lafefspietz/noiseotron/3dprint/pluto-bracket-base-drawing.png

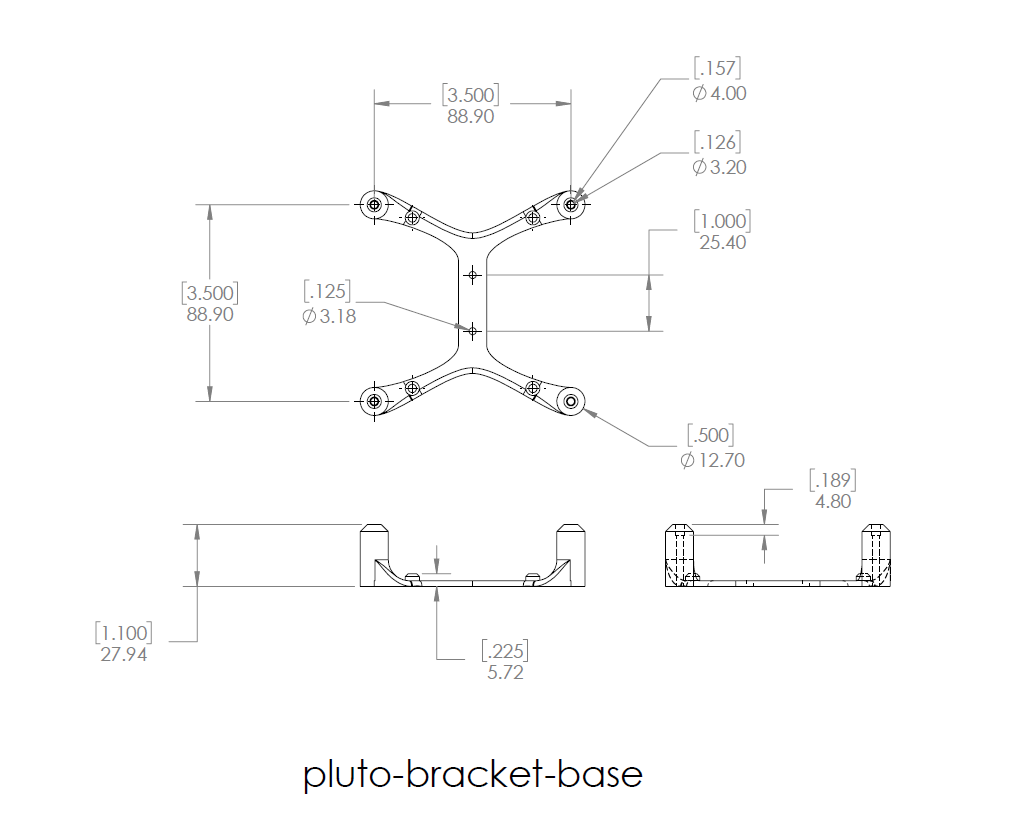
3dprint/pluto-bracket-base-drawing.png
