lafefspietz/noiseotron/3dprint/pluto-bracket-top-bar-drawing.png

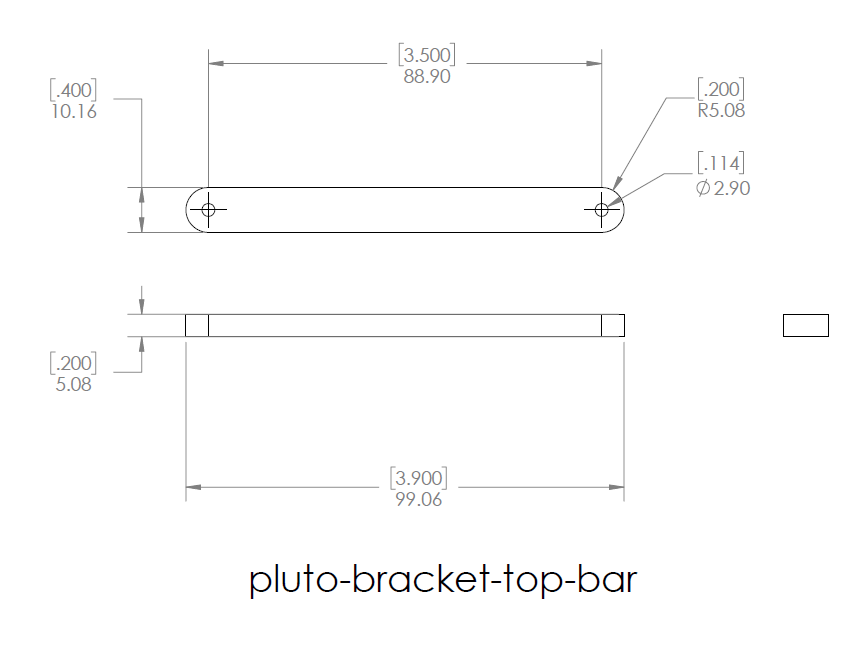
3dprint/pluto-bracket-top-bar-drawing.png
