lafefspietz/noiseotron/3dprint/stemma-knob-wood-bracket-drawing.png

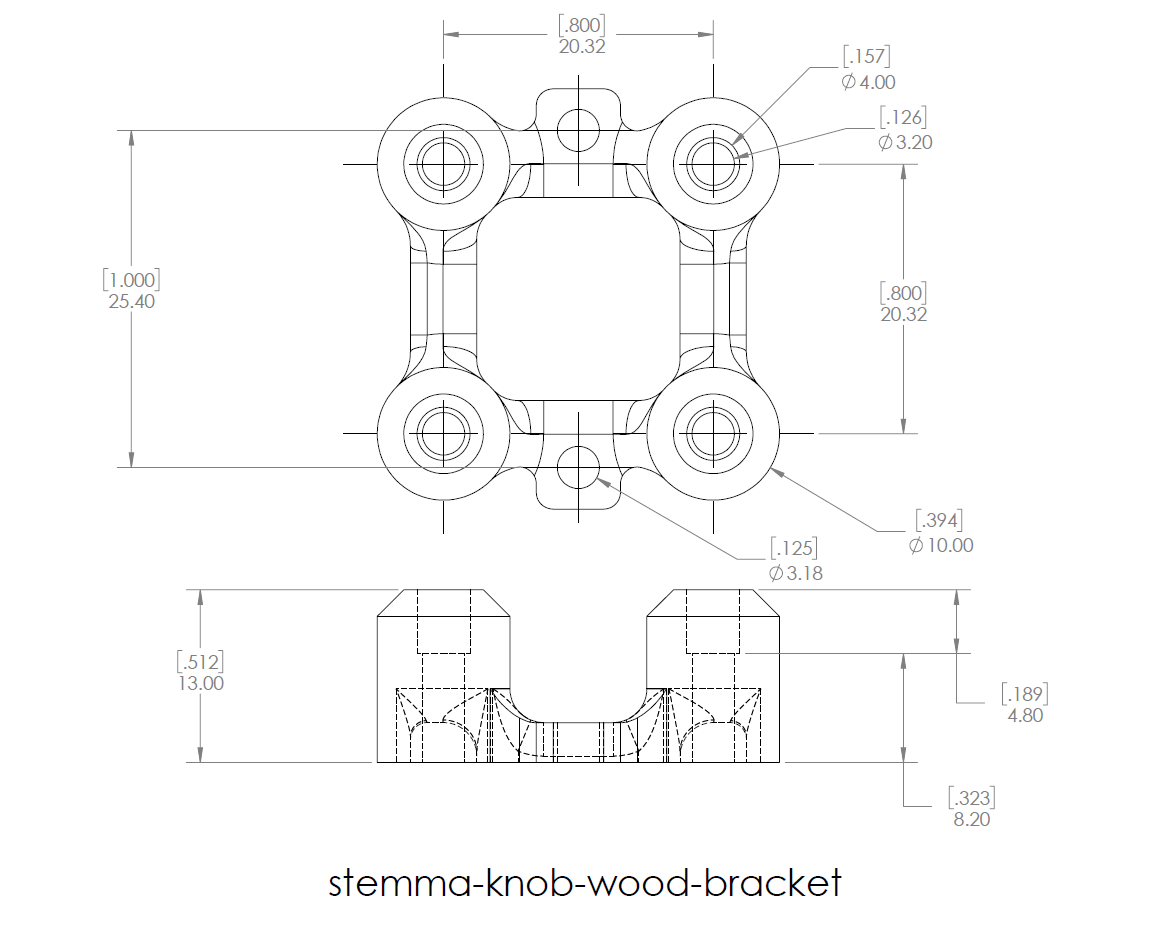
3dprint/stemma-knob-wood-bracket-drawing.png
