lafefspietz/noiseotron/3dprint/string-anchor-drawing.png

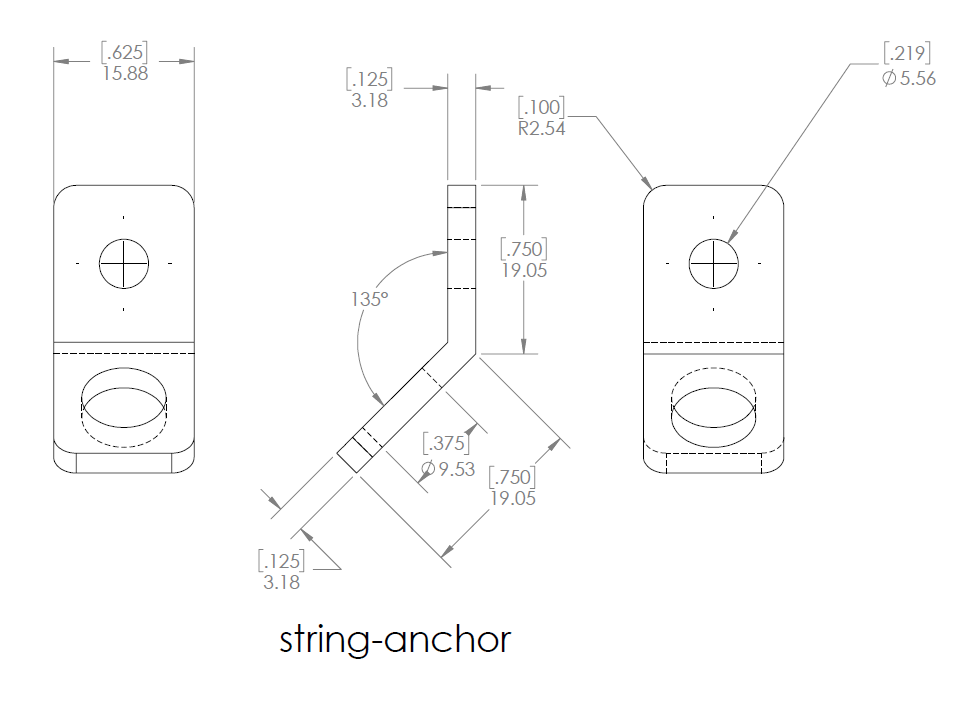
3dprint/string-anchor-drawing.png
