lafefspietz/noiseotron/3dprint/wood-angle-bracket-drawing.png

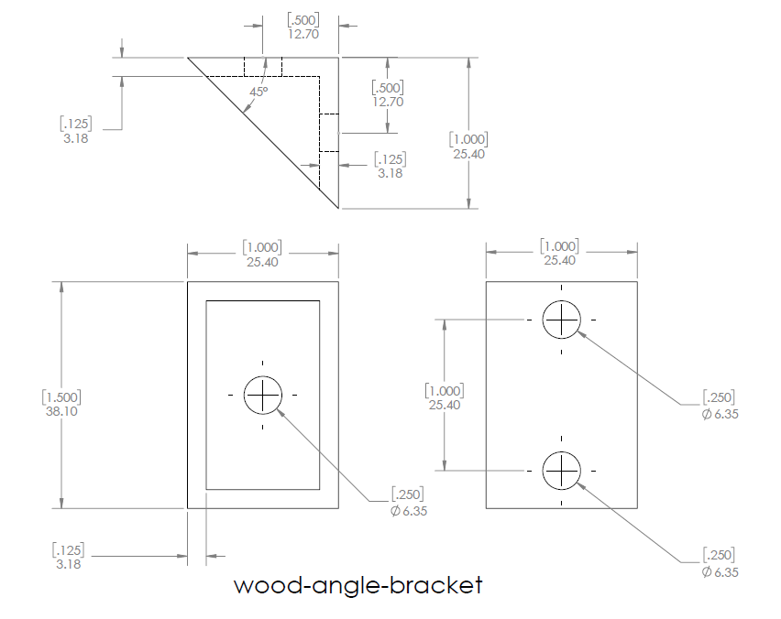
3dprint/wood-angle-bracket-drawing.png
