lafefspietz/noiseotron/3dprint/wood-peg-drawing.png

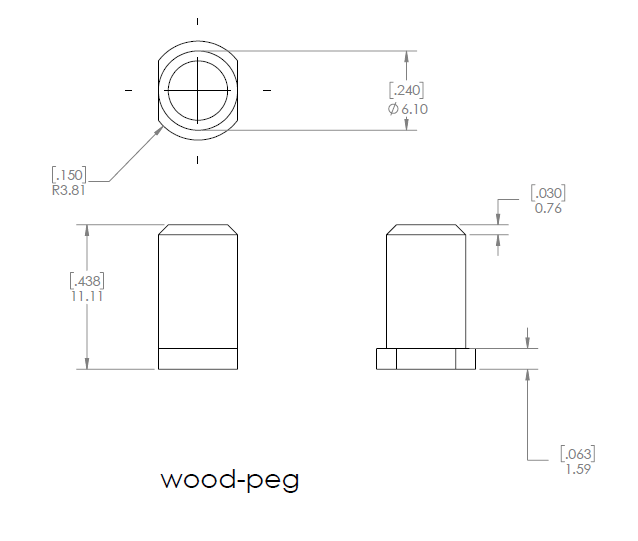
3dprint/wood-peg-drawing.png
