lafefspietz/noiseotron/geometron/symbolfeed/symbol1725227815.png

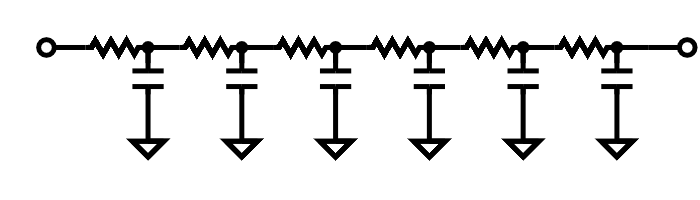
geometron/symbolfeed/symbol1725227815.png
