lafefspietz/noiseotron/geometron/symbolfeed/symbol1725228691.png

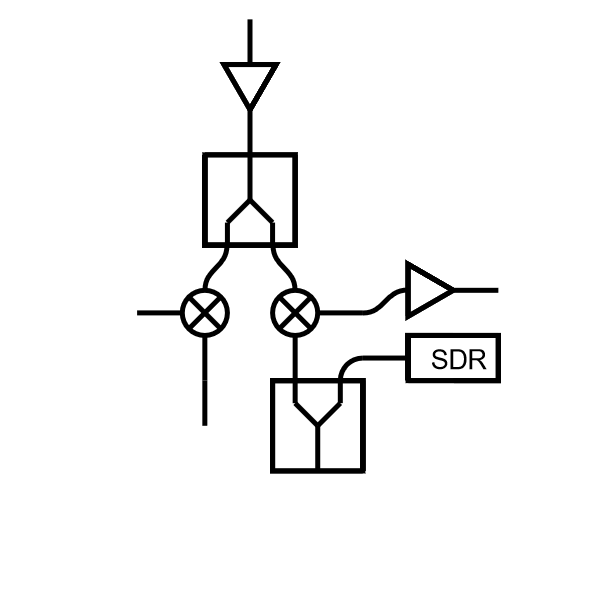
geometron/symbolfeed/symbol1725228691.png
