lafefspietz/noiseotron/geometron/symbolfeed/symbol1725228702.png

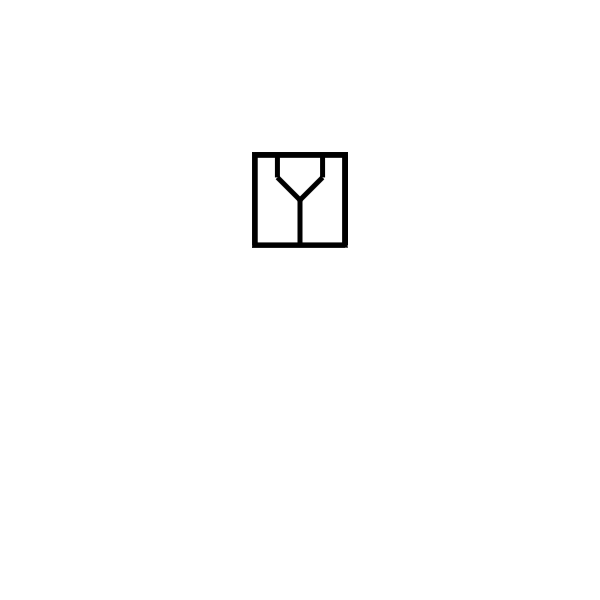
geometron/symbolfeed/symbol1725228702.png
