lafefspietz/noiseotron/geometron/symbolfeed/symbol1725229308.png

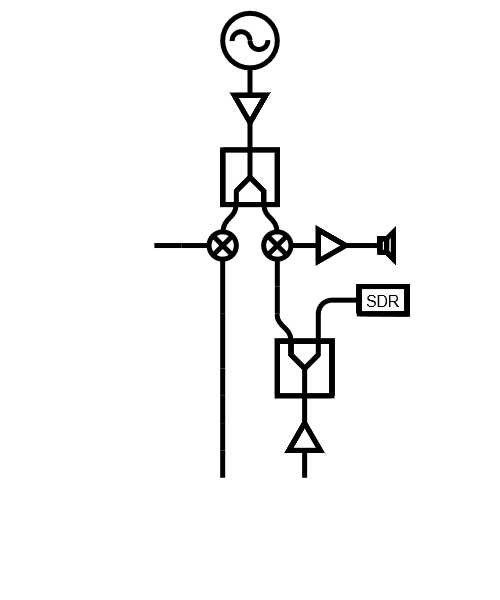
geometron/symbolfeed/symbol1725229308.png
