lafefspietz/noiseotron/geometron/symbolfeed/symbol1725230151.png

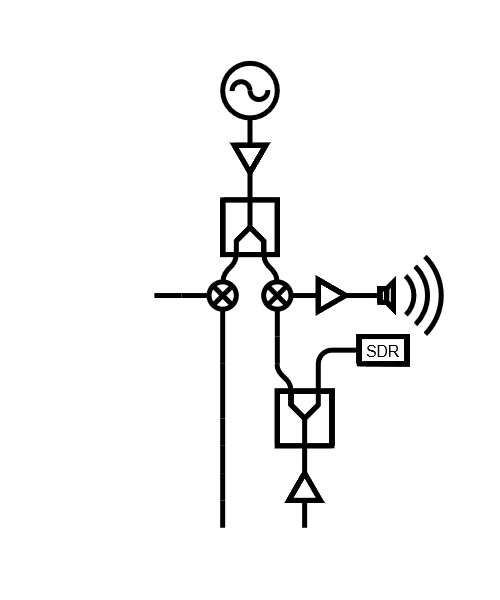
geometron/symbolfeed/symbol1725230151.png
