lafefspietz/noiseotron/geometron/symbolfeed/symbol1725230180.png

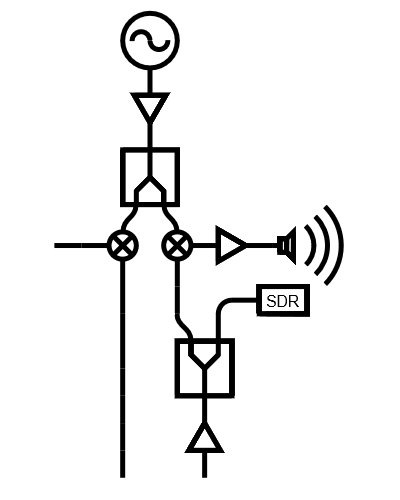
geometron/symbolfeed/symbol1725230180.png
