lafefspietz/noiseotron/geometron/symbolfeed/symbol1725233175.png

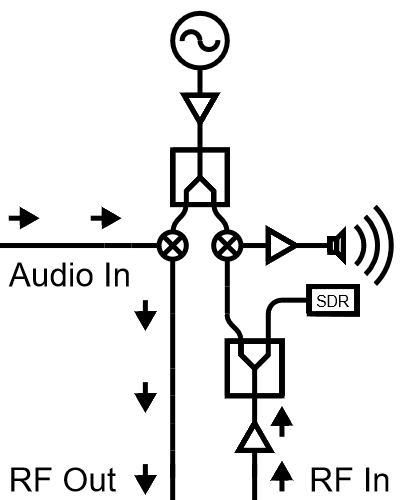
geometron/symbolfeed/symbol1725233175.png
