lafefspietz/noiseotron/geometron/symbolfeed/symbol1725233252.png

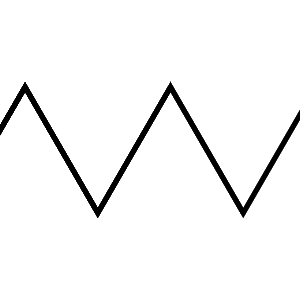
geometron/symbolfeed/symbol1725233252.png
