lafefspietz/noiseotron/geometron/symbolfeed/symbol1725233533.png

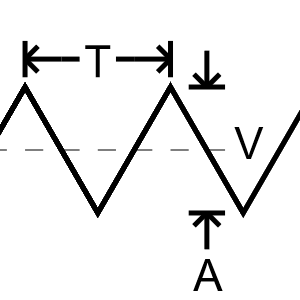
geometron/symbolfeed/symbol1725233533.png
