lafefspietz/noiseotron/geometron/symbolfeed/symbol1725308124.png

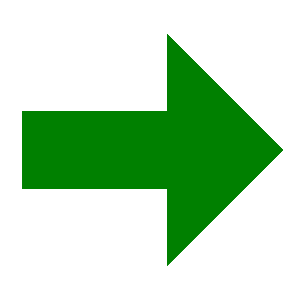
geometron/symbolfeed/symbol1725308124.png
