lafefspietz/noiseotron/geometron/symbolfeed/symbol1725309059.png

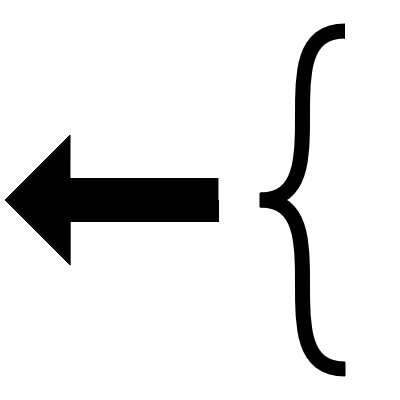
geometron/symbolfeed/symbol1725309059.png
