lafefspietz/noiseotron/geometron/symbolfeed/symbol1725309077.png

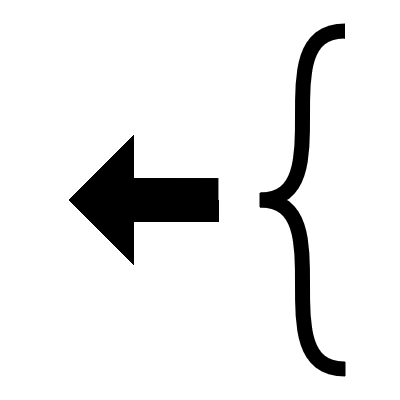
geometron/symbolfeed/symbol1725309077.png
