lafefspietz/noiseotron/geometron/symbolfeed/symbol1725309135.png

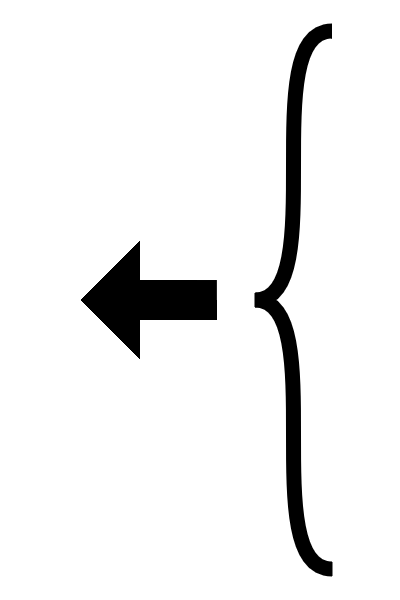
geometron/symbolfeed/symbol1725309135.png
