lafefspietz/noiseotron/geometron/symbolfeed/symbol1725373750.png

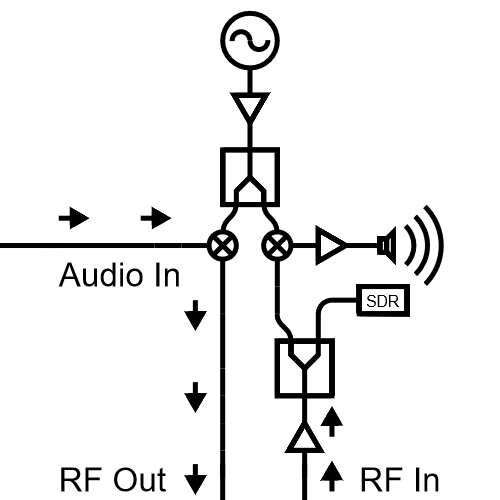
geometron/symbolfeed/symbol1725373750.png
