lafefspietz/noiseotron/geometron/symbolfeed/symbol1725374171.png

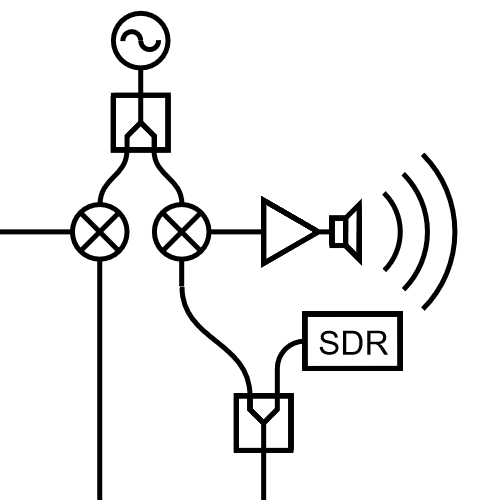
geometron/symbolfeed/symbol1725374171.png
