lafefspietz/noiseotron/geometron/symbolfeed/symbol1725374411.png

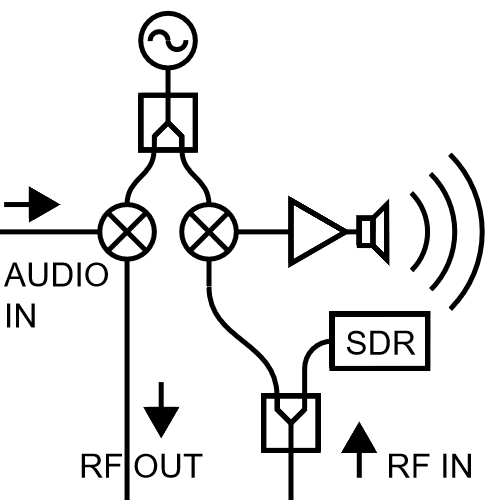
geometron/symbolfeed/symbol1725374411.png
