lafefspietz/noiseotron/geometron/symbolfeed/symbol1725385577.png

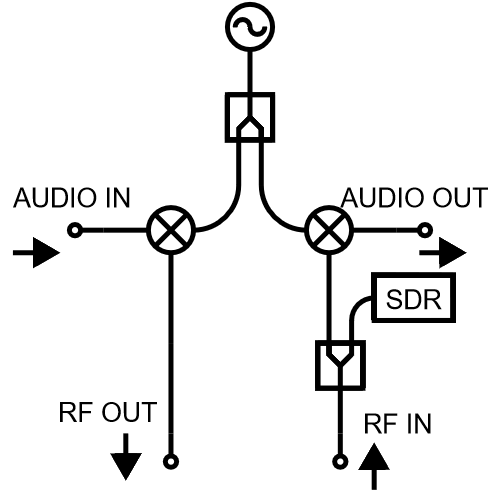
geometron/symbolfeed/symbol1725385577.png
