lafefspietz/noiseotron/geometron/symbolfeed/symbol1725396129.png

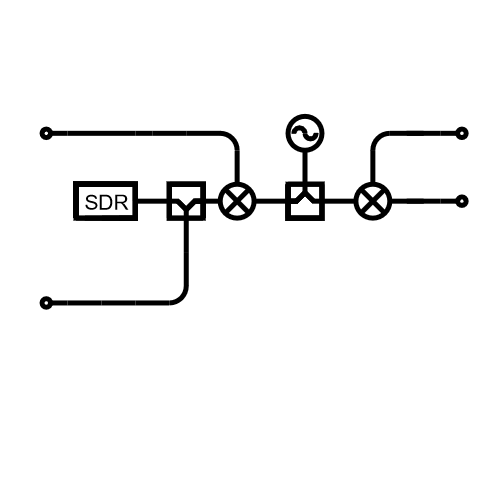
geometron/symbolfeed/symbol1725396129.png
