lafefspietz/noiseotron/geometron/symbolfeed/symbol1725396302.png

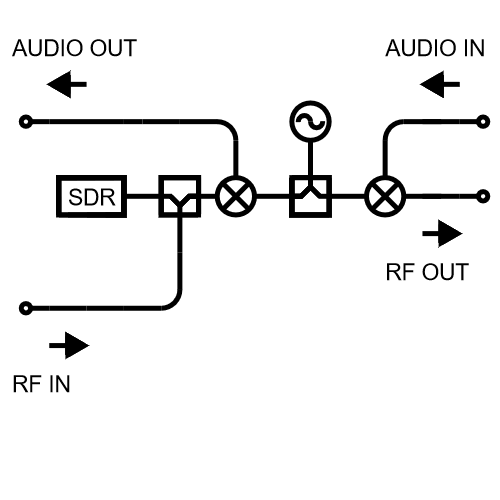
geometron/symbolfeed/symbol1725396302.png
