lafefspietz/noiseotron/images/blueknob.png

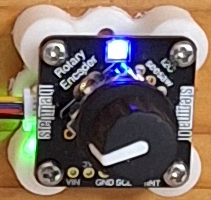
images/blueknob.png
