lafefspietz/noiseotron/images/knobimage.png

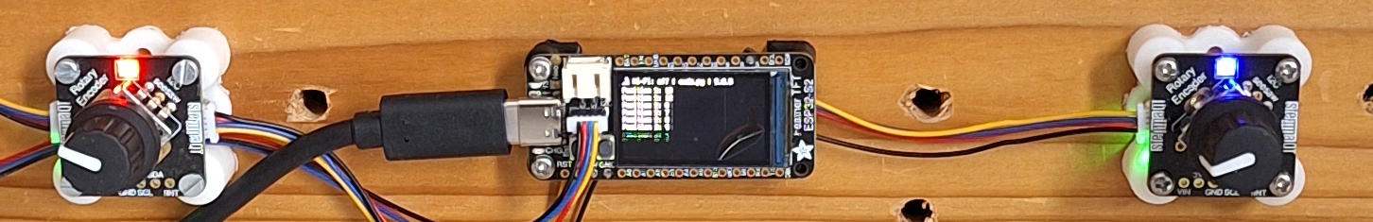
images/knobimage.png
