lafefspietz/noiseotron/images/noise-red.png

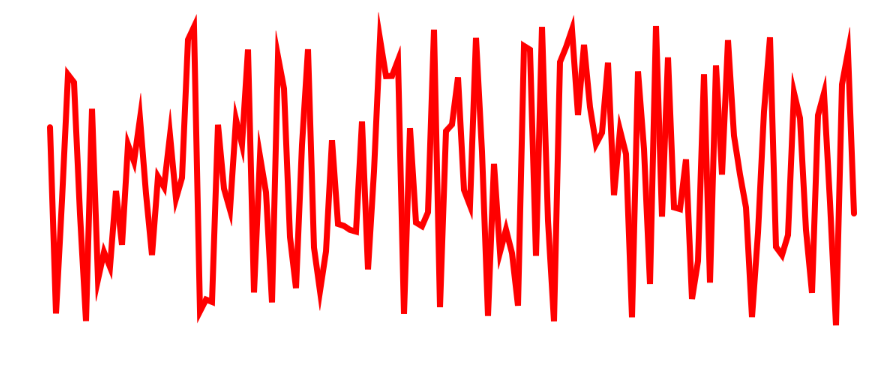
images/noise-red.png
