lafefspietz/noiseotron/images/noise.png

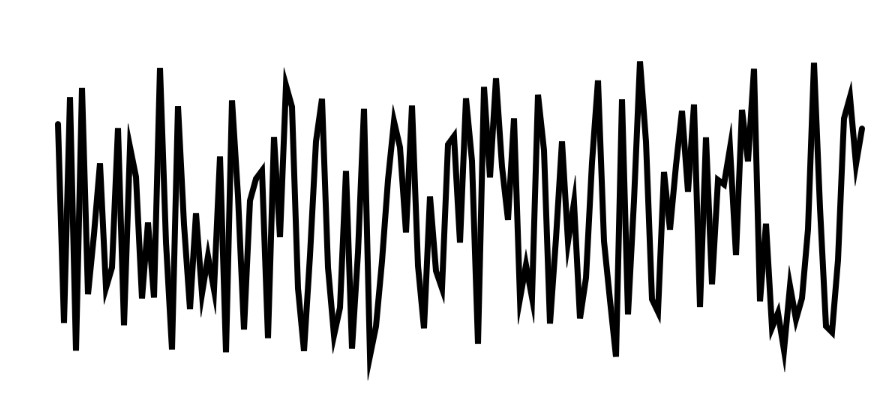
images/noise.png
