lafefspietz/noiseotron/images/rack-side-holes-model.png

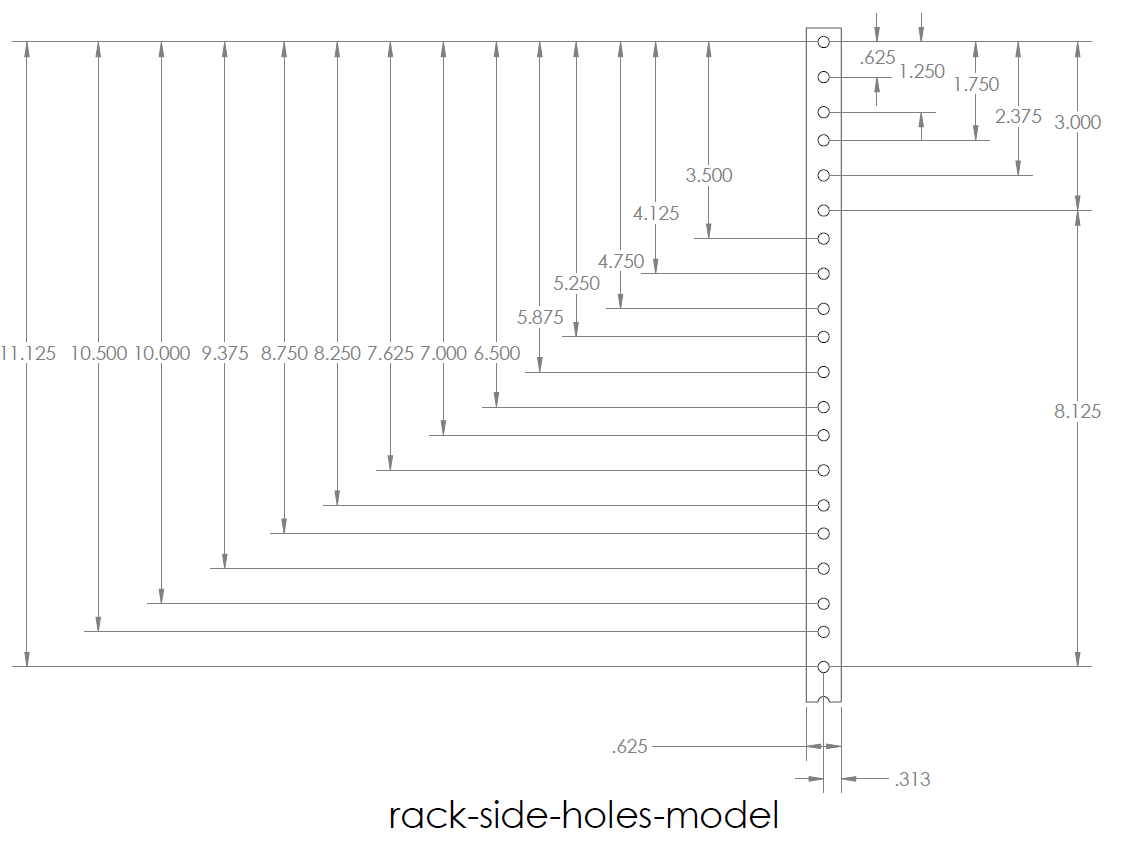
images/rack-side-holes-model.png
