lafefspietz/noiseotron/images/rackmount-front-render.png

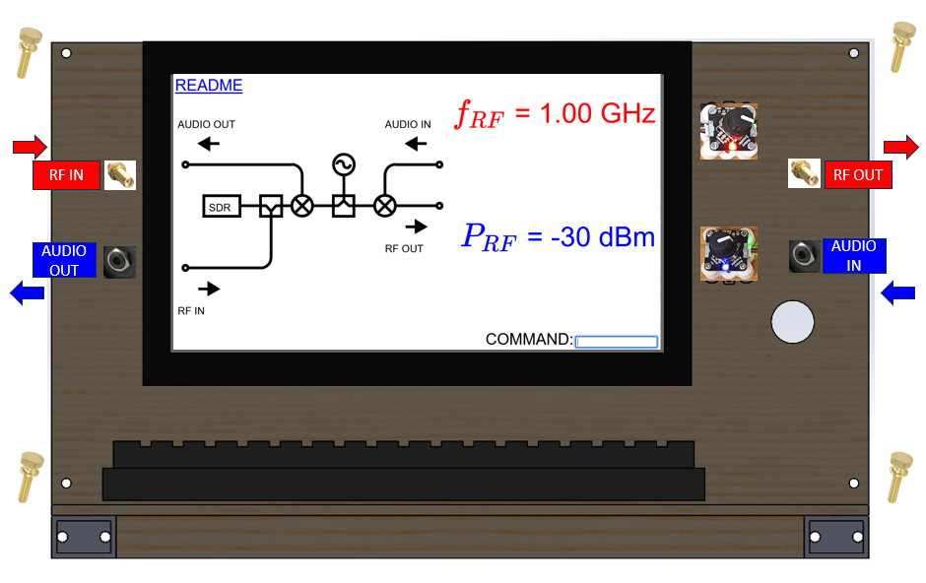
images/rackmount-front-render.png
