lafefspietz/noiseotron/images/radio-html-screenshot.png

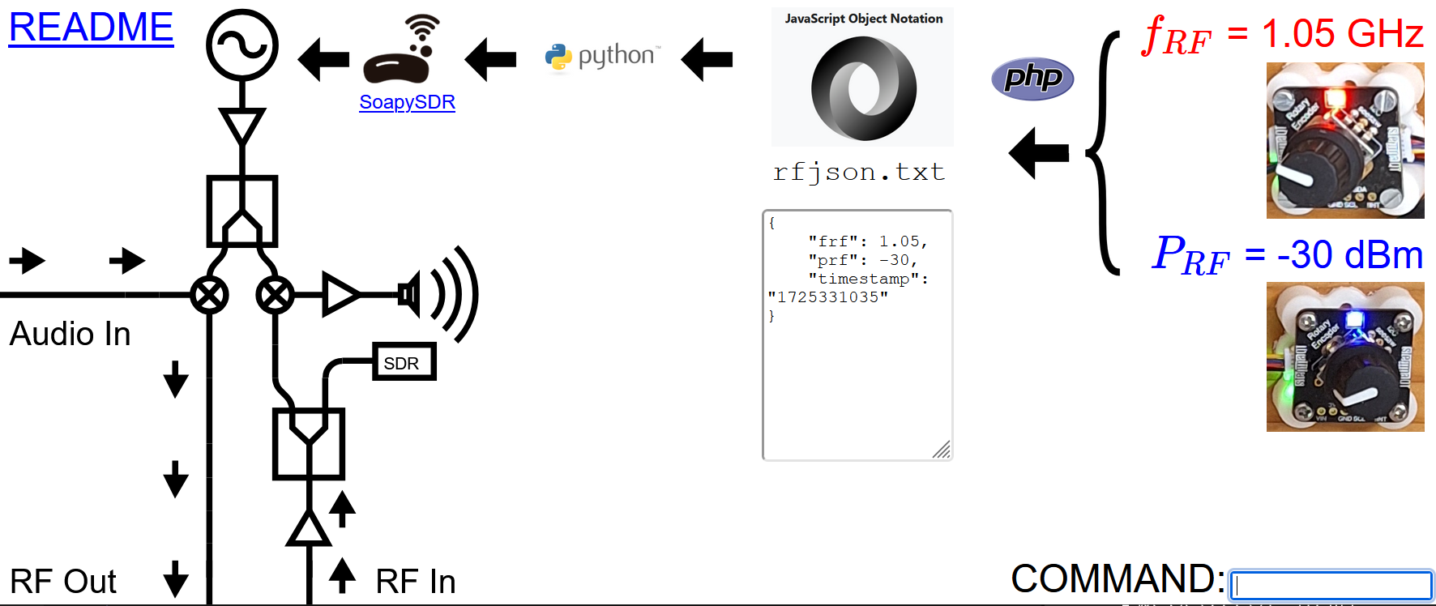
images/radio-html-screenshot.png
