lafefspietz/noiseotron/images/redknob.png

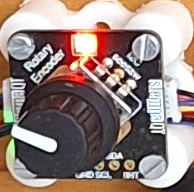
images/redknob.png
