lafefspietz/noiseotron/images/rf-block-diagram.png

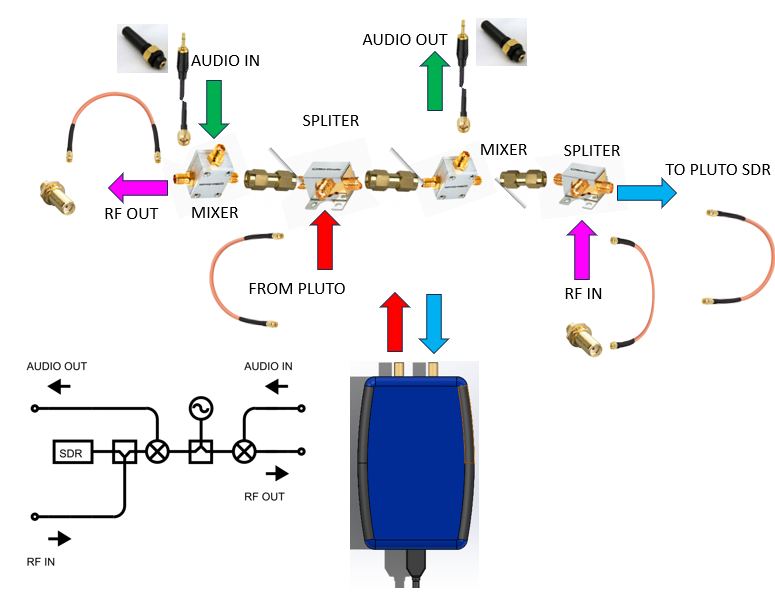
images/rf-block-diagram.png
