lafefspietz/noiseotron/images/sine-blue.png

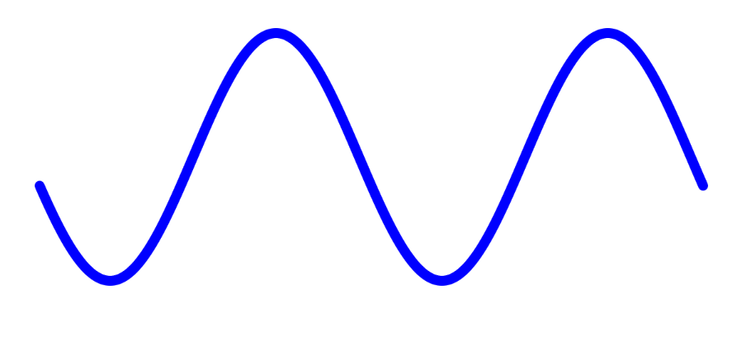
images/sine-blue.png
