lafefspietz/noiseotron/wood/keyboard-shelf-drawing.png

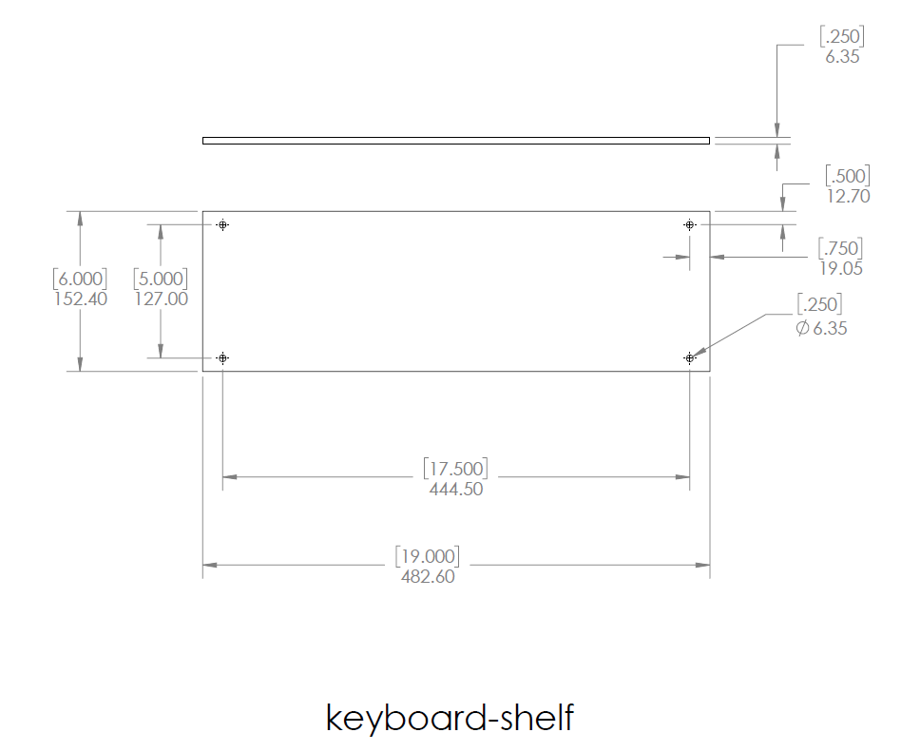
wood/keyboard-shelf-drawing.png
