lafefspietz/noiseotron/wood/rack-mount-panel-drawing.png

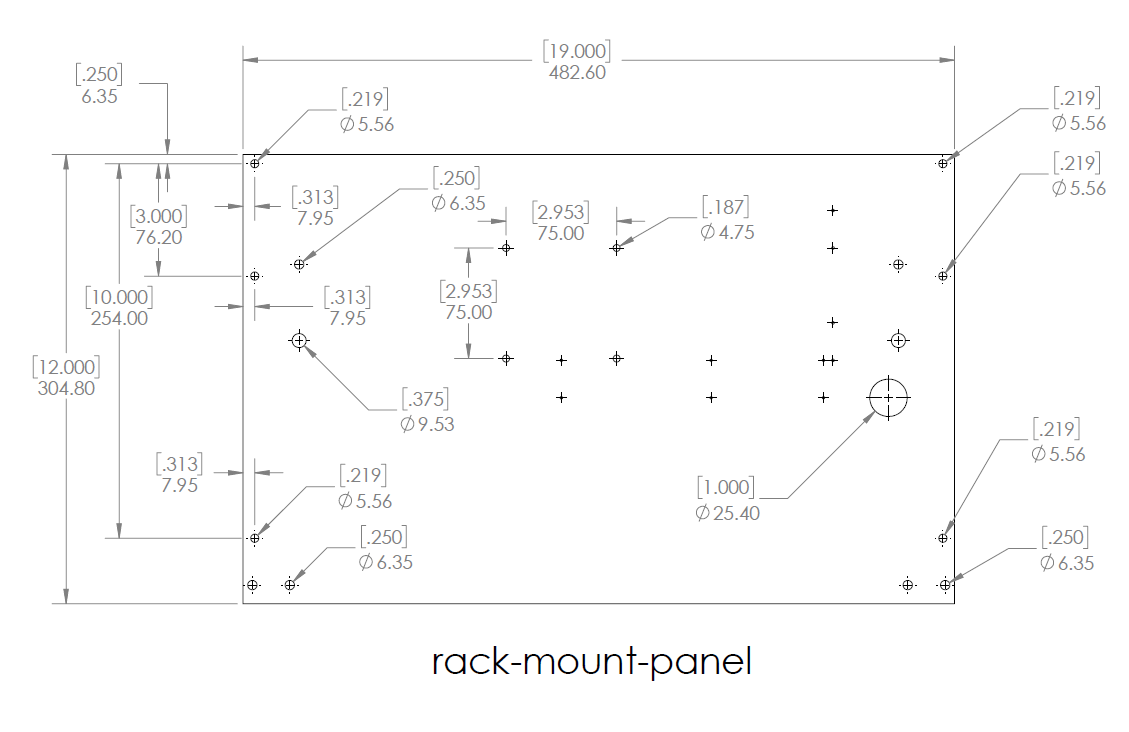
wood/rack-mount-panel-drawing.png
