lafefspietz/noiseotron/3dprint/wood-angle-bracket-top.SLDPRT

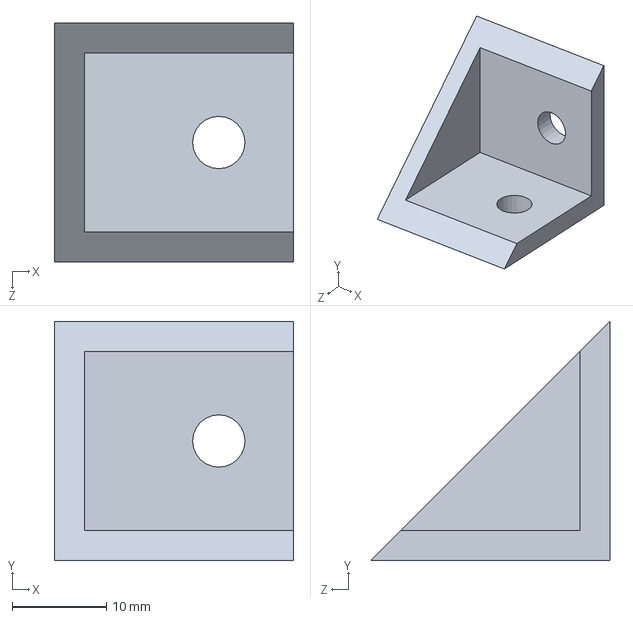
[picture p71: CAD file, 2024-09-05]
3dprint/wood-angle-bracket-top.SLDPRT
25.4 x 25.4 x 25.4 mm
