lafefspietz/noiseotron/3dmodel/pluto-box-model.SLDPRT

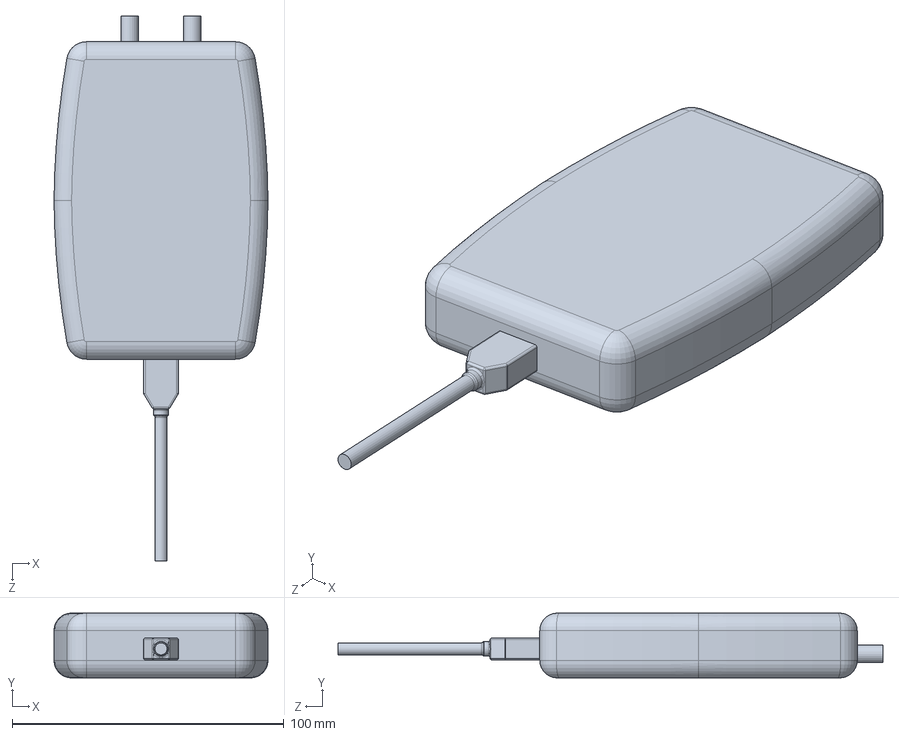
[picture p72: CAD file, 2024-09-02]
3dmodel/pluto-box-model.SLDPRT
78.7 x 23.9 x 200.4 mm
