lafefspietz/noiseotron/3dprint/wood-peg.SLDPRT

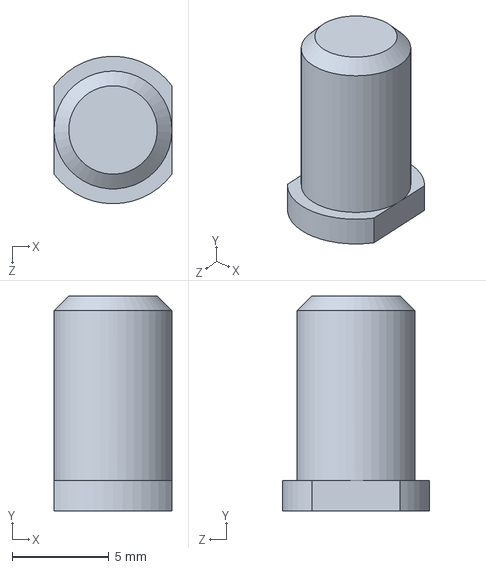
[picture p73: CAD file, 2024-09-02]
3dprint/wood-peg.SLDPRT
6.10 x 11.1 x 7.62 mm
