lafefspietz/noiseotron/3dmodel/screen.SLDPRT

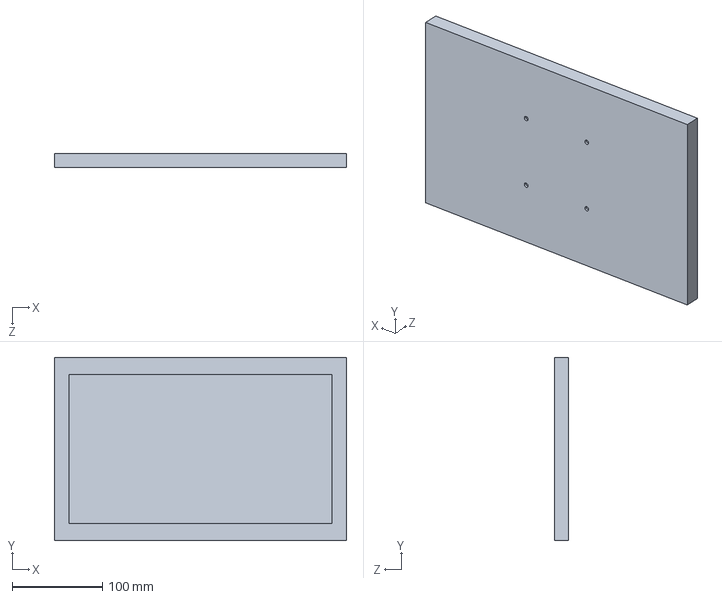
[picture p74: CAD file, 2024-09-02]
3dmodel/screen.SLDPRT
323.9 x 203.2 x 15.9 mm
