lafefspietz/noiseotron/3dprint/woodpi.STEP

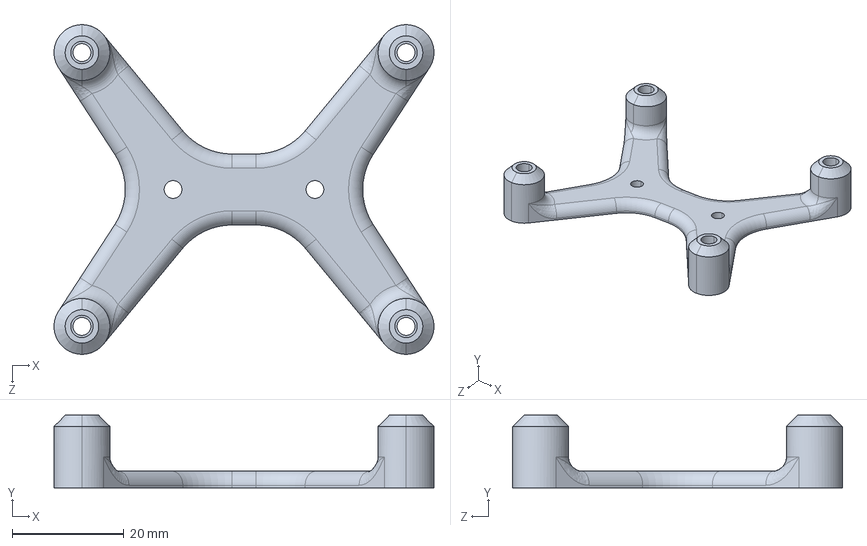
[picture p75: CAD file, 2024-09-02]
3dprint/woodpi.STEP
68.0 x 13.0 x 59.0 mm
