lafefspietz/noiseotron/3dmodel/keyboard.SLDPRT

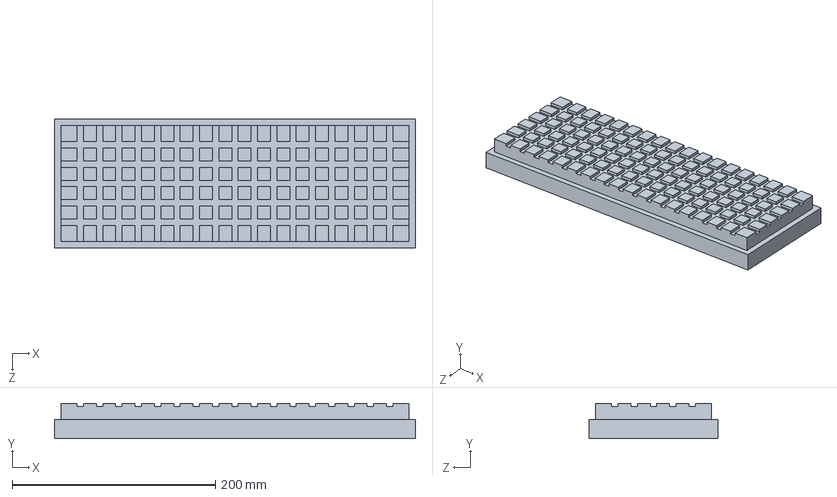
[picture p76: CAD file, 2024-09-02]
3dmodel/keyboard.SLDPRT
355.6 x 34.9 x 127.0 mm
