lafefspietz/noiseotron/3dprint/wood-angle-bracket.SLDPRT

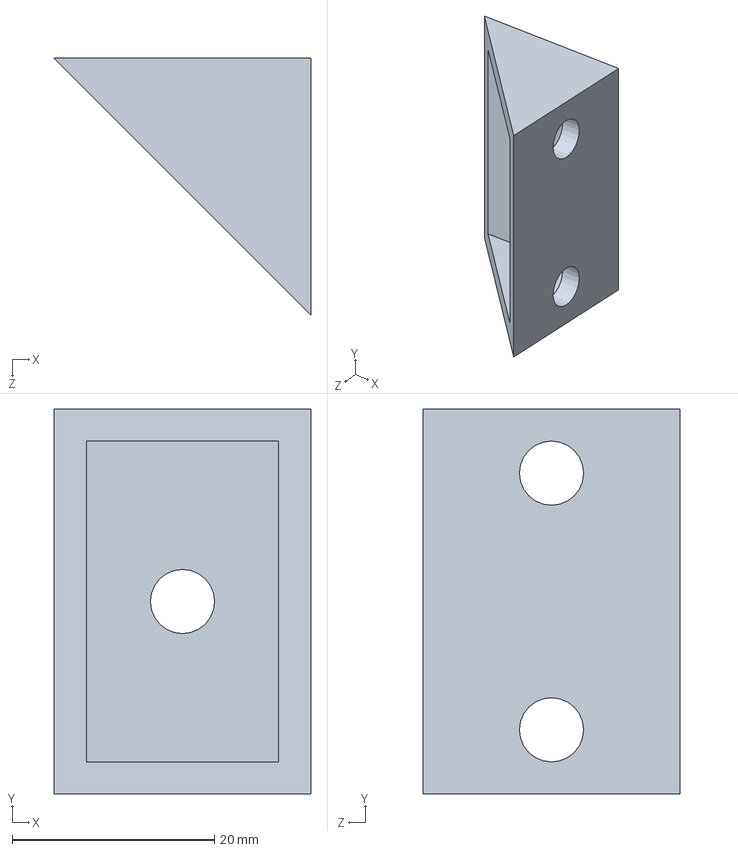
[picture p77: CAD file, 2024-09-02]
3dprint/wood-angle-bracket.SLDPRT
25.4 x 38.1 x 25.4 mm
