lafefspietz/noiseotron/3dmodel/paracord.SLDPRT

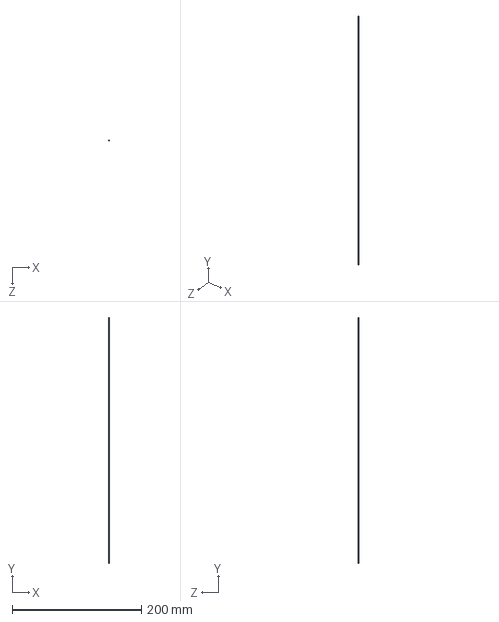
[picture p78: CAD file, 2024-09-02]
3dmodel/paracord.SLDPRT
1.52 x 381.0 x 1.52 mm
